butrejp/hgr/config-20251417/config/macro_start_end.cfg

[gcode_macro PRINT_START]
gcode:
  {% set BED = params.BED_TEMP|int %}
  {% set EXTRUDER = params.EXTRUDER_TEMP|int %}
  M104 S160 ;Start heating extruder
  M190 S{BED}  ;Set bed temperature and wait
  G28
  Z_TILT_ADJUST
  G28 Z
  BED_MESH_PROFILE LOAD=default  ;Load Bed Mesh Profile
  g0 x0 y0 z0.28
  M109 S{EXTRUDER}  ;Set extruder temperature and wait
  _PURGE_LINE  ;Front Purge
  G90  ;Set to absolute positioning
  G92 E0   ;Reset extruder

[gcode_macro PRINT_END]
gcode:
  M400  ;Clear buffer
  G90  ;Set to absolute positioning
  _MOVE_AWAY  ;Move away from print
  G92 E0   ;Reset extruder
  G1 F-25 F1800  ;Retract filament
  TURN_OFF_HEATERS  ;Turn off heaters
  PARK_CENTER_REAR  ;Park central rear
  M84  ;Disable motors

[gcode_macro _PURGE_LINE]
gcode:
  {% if printer["gcode_macro status_cleaning"] != null %}
    status_cleaning
  {% endif %}
  SAVE_GCODE_STATE NAME=Pre_Prime
        
  G90
  G92 E0 ;Reset Extruder

  G1 Z0.28 F5000.0 ;Move to start position
  G1 X0 Y100 Z0.28 F2500.0 E20 ;Draw the first line
  G1 X0.4 F2500.0 ;move over
  G1 X0.4 Y0 Z0.28 F2500.0 E40 ;Draw the second line
  G92 E0 ;Reset Extruder
  G1 Z10 F3000 ;Move Z Axis up
  RESTORE_GCODE_STATE NAME=Pre_Prime

  {% if printer["gcode_macro status_printing"] != null %}
    status_printing
  {% endif %}


[gcode_macro _MOVE_AWAY]
gcode:
    {% set th = printer.toolhead %}
    {% set x_safe = th.position.x + 20 * (1 if th.axis_maximum.x - th.position.x > 20 else -1) %}
    {% set y_safe = th.position.y + 20 * (1 if th.axis_maximum.y - th.position.y > 20 else -1) %}
    {% set z_safe = [th.position.z + 2, th.axis_maximum.z]|min %}
      
    G90                                      ; absolute positioning
    G0 X{x_safe} Y{y_safe} Z{z_safe} F20000  ; move nozzle to remove stringing


[gcode_macro PARK_CENTER_REAR]
gcode:
    {% if printer["gcode_macro status_busy"] != null %}
      status_busy
    {% endif %}
    {% set th = printer.toolhead %}
    {% set x_safe = th.position.x + 20 * (1 if th.axis_maximum.x - th.position.x > 20 else -1) %}
    {% set y_safe = th.position.y + 20 * (1 if th.axis_maximum.y - th.position.y > 20 else -1) %}

    G0 X{th.axis_maximum.x//2} Y{th.axis_maximum.y - 2} F3600  
    {% if printer["gcode_macro status_ready"] != null %}
    status_ready
    {% endif %}
